ctcl-bregis/mct2/full/case/mct2_smec_smd.scad

// MediaCow Touch 2 - CTCL 2021-2025
// Purpose: SMEC display mount
// Created: February 12, 2025
// Modified: February 12, 2025
