ctcl-bregis/mct2/circuits/mct2/mct2_power.kicad_sch

## KiCad design circuits/mct2/mct2_power.kicad_sch (2024-09-12)

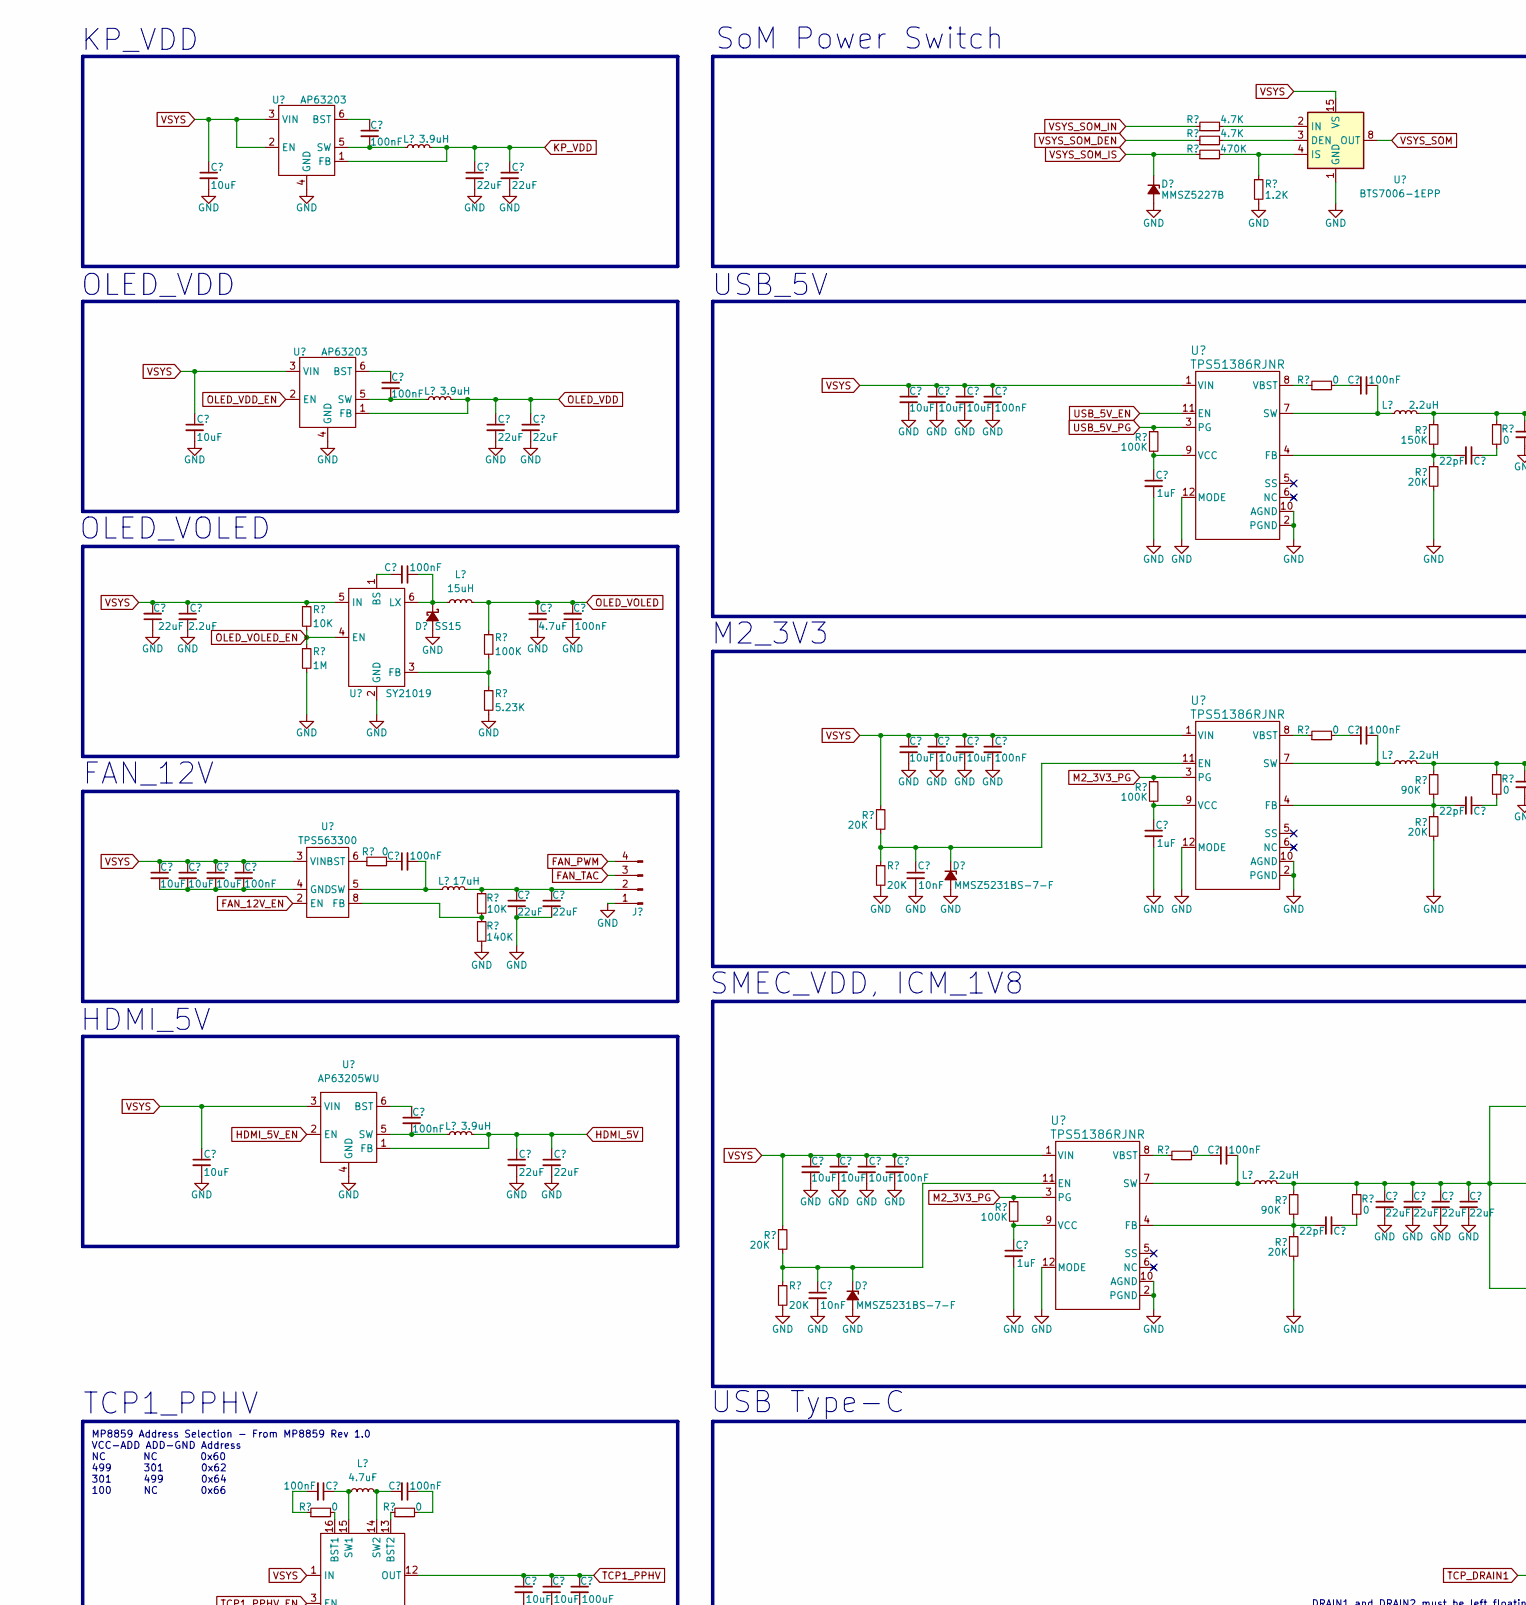
[picture p9: schematic mct2_power.kicad_sch, part in row 1, column 1]

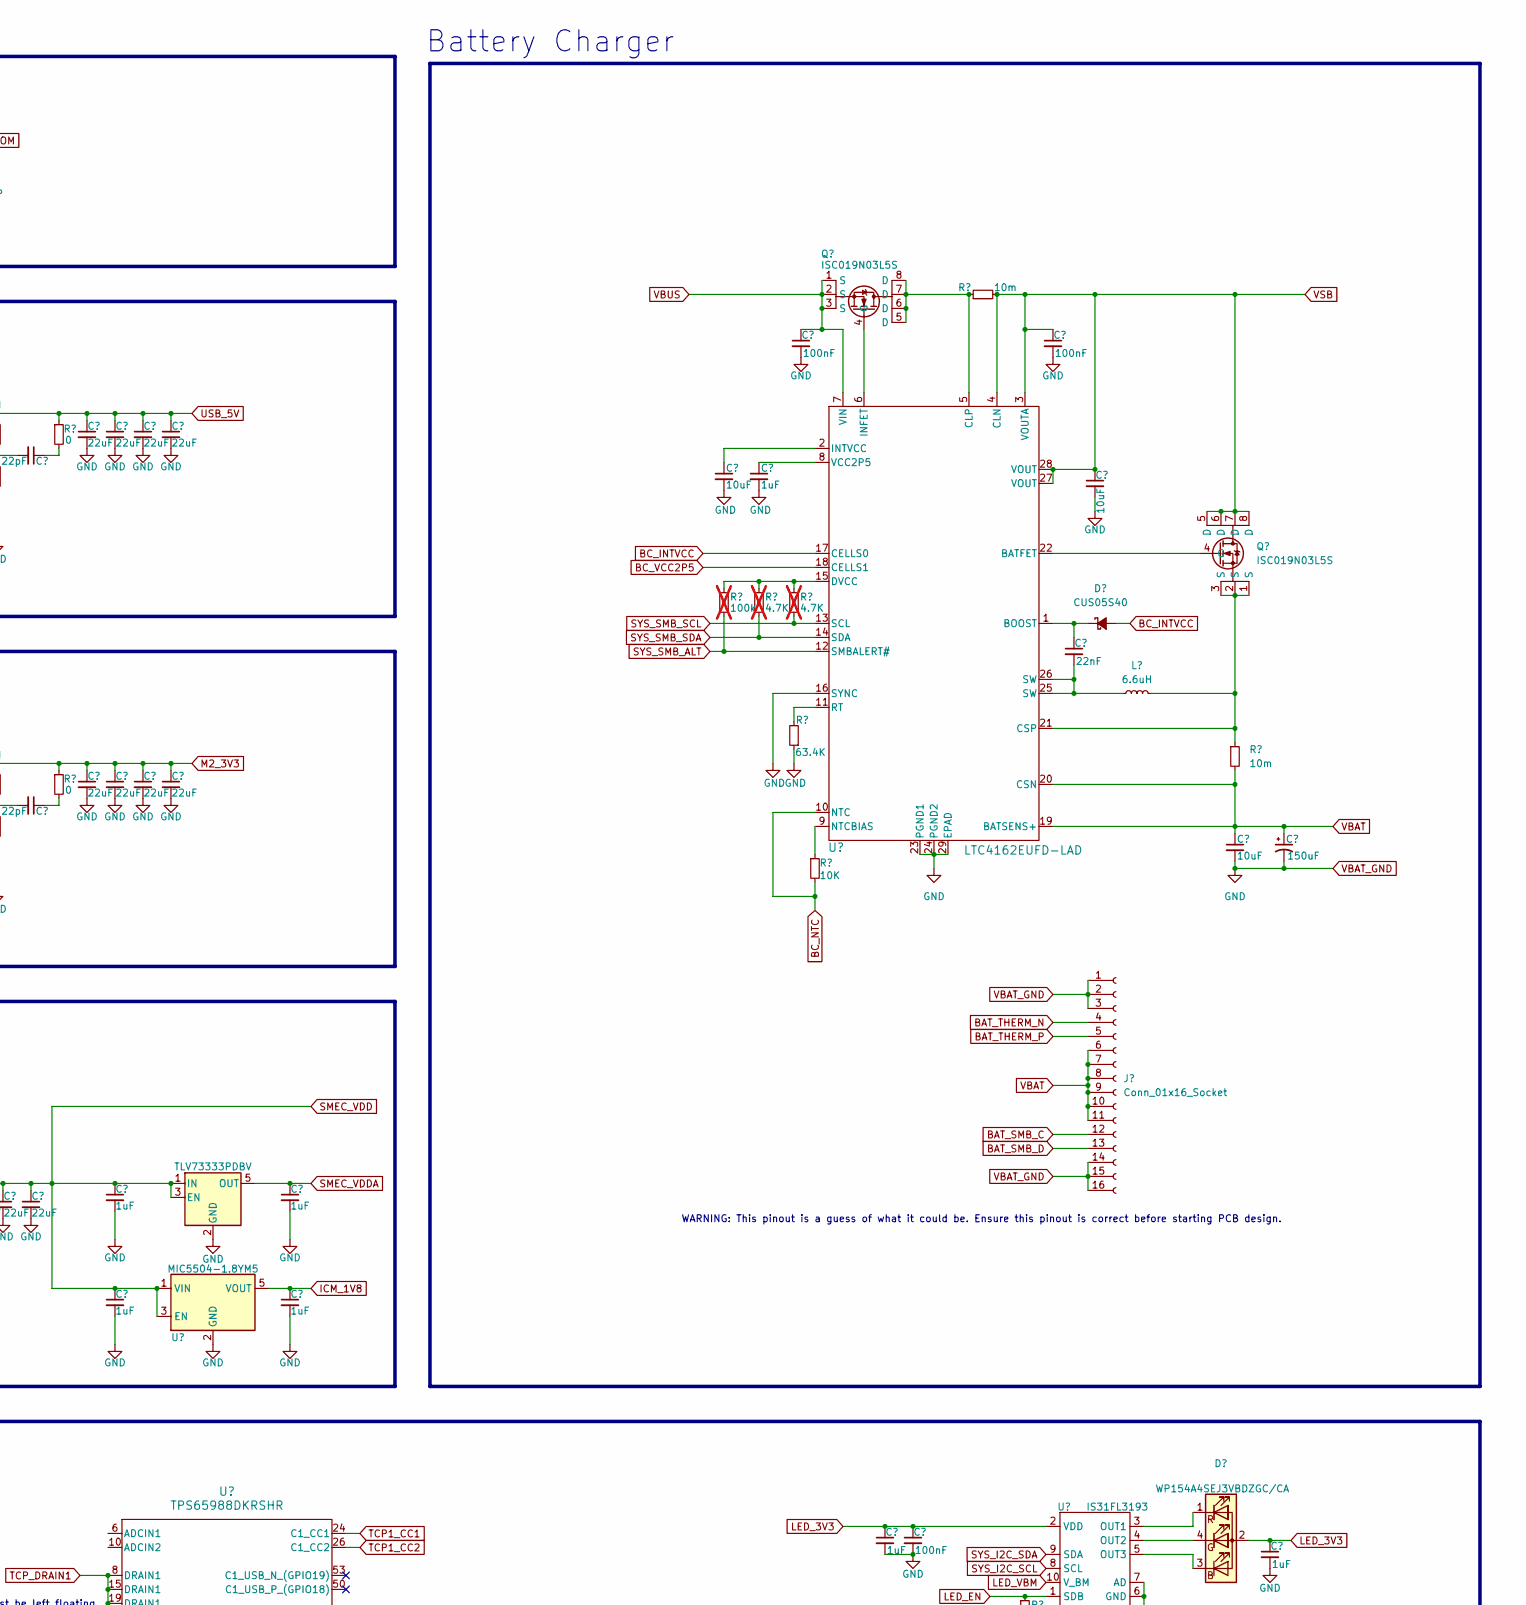
[picture p10: schematic mct2_power.kicad_sch, part in row 1, column 2]

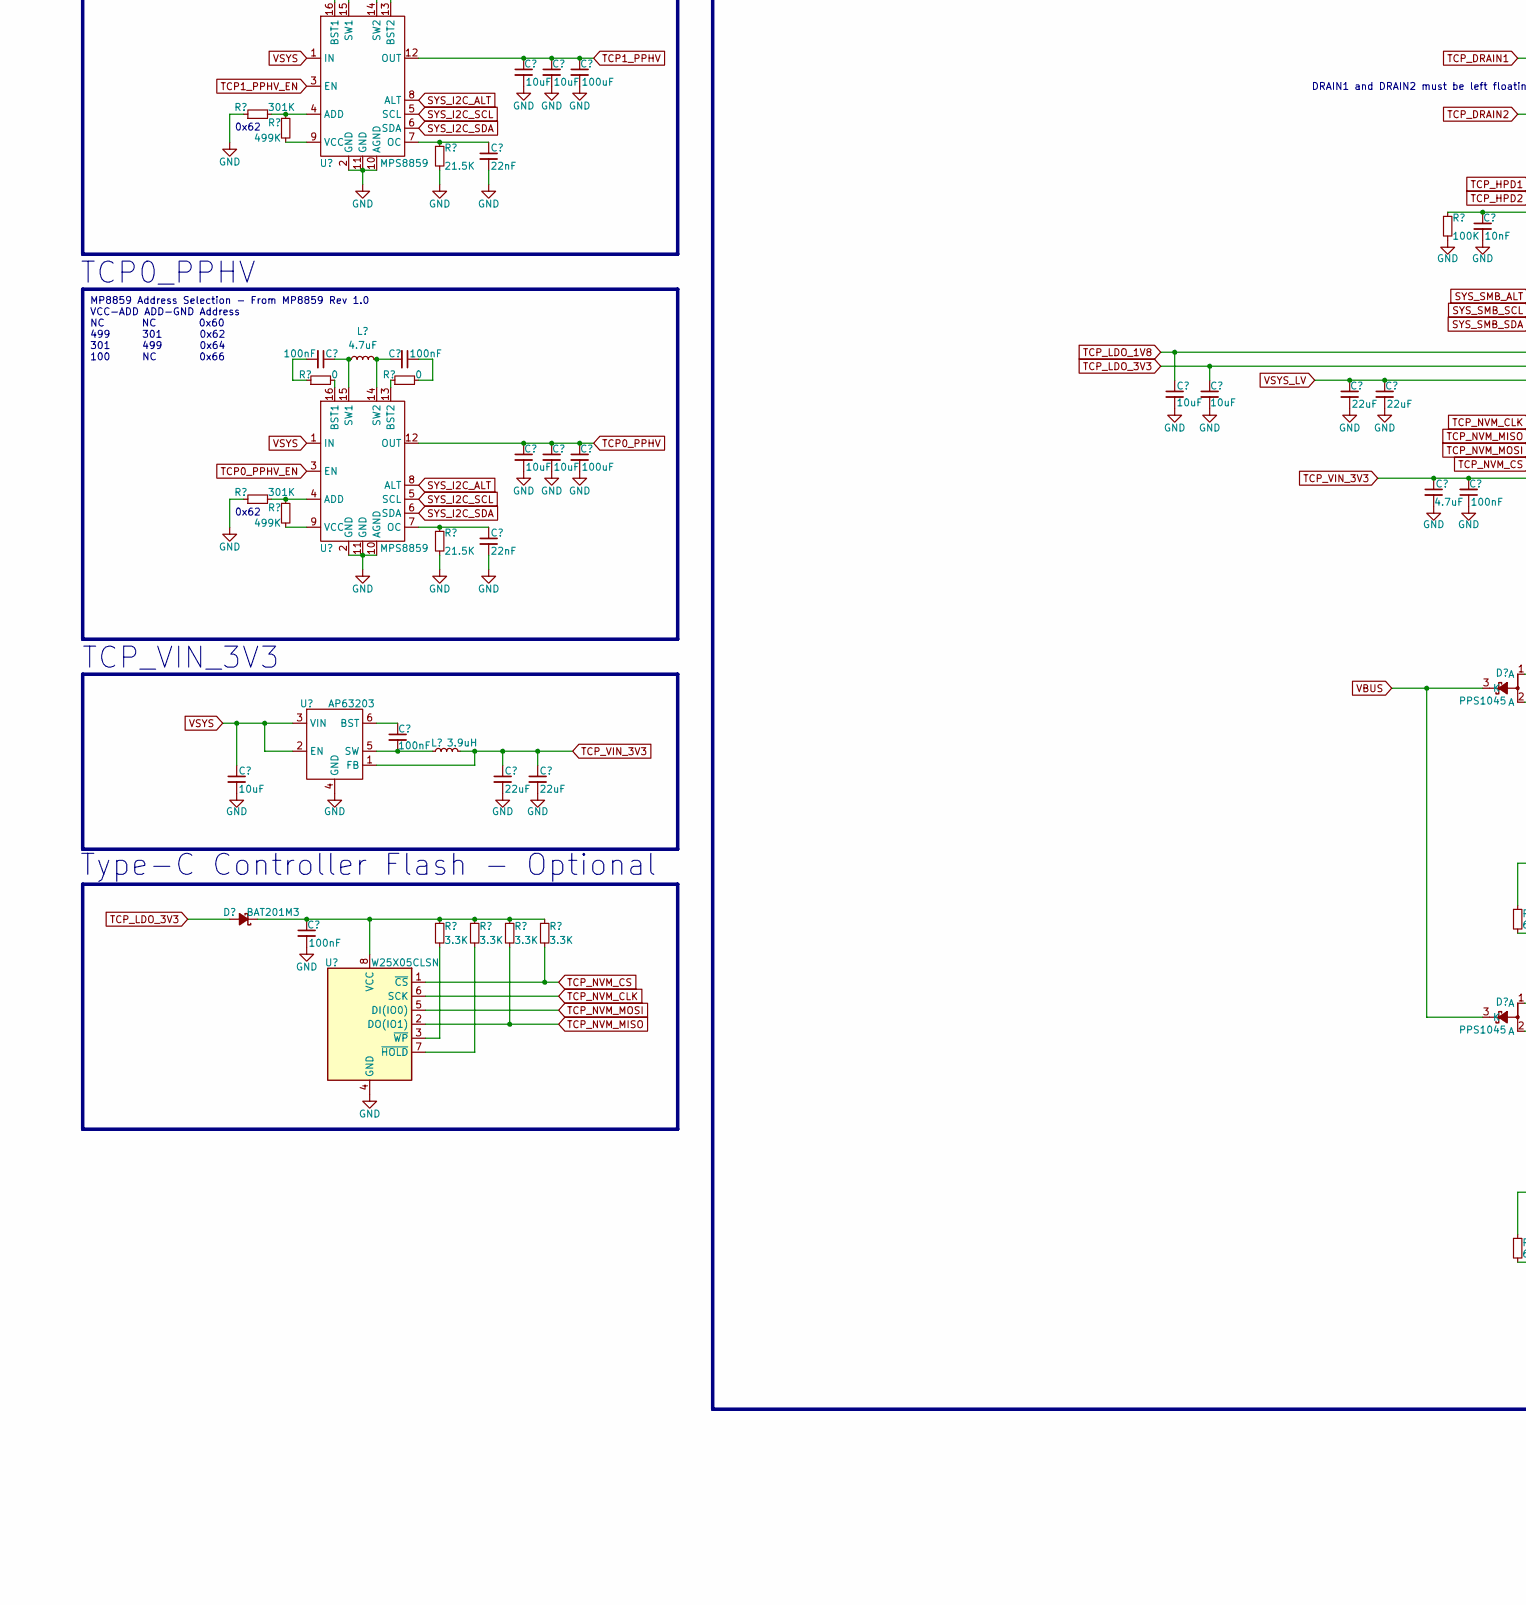
[picture p11: schematic mct2_power.kicad_sch, part in row 2, column 1]

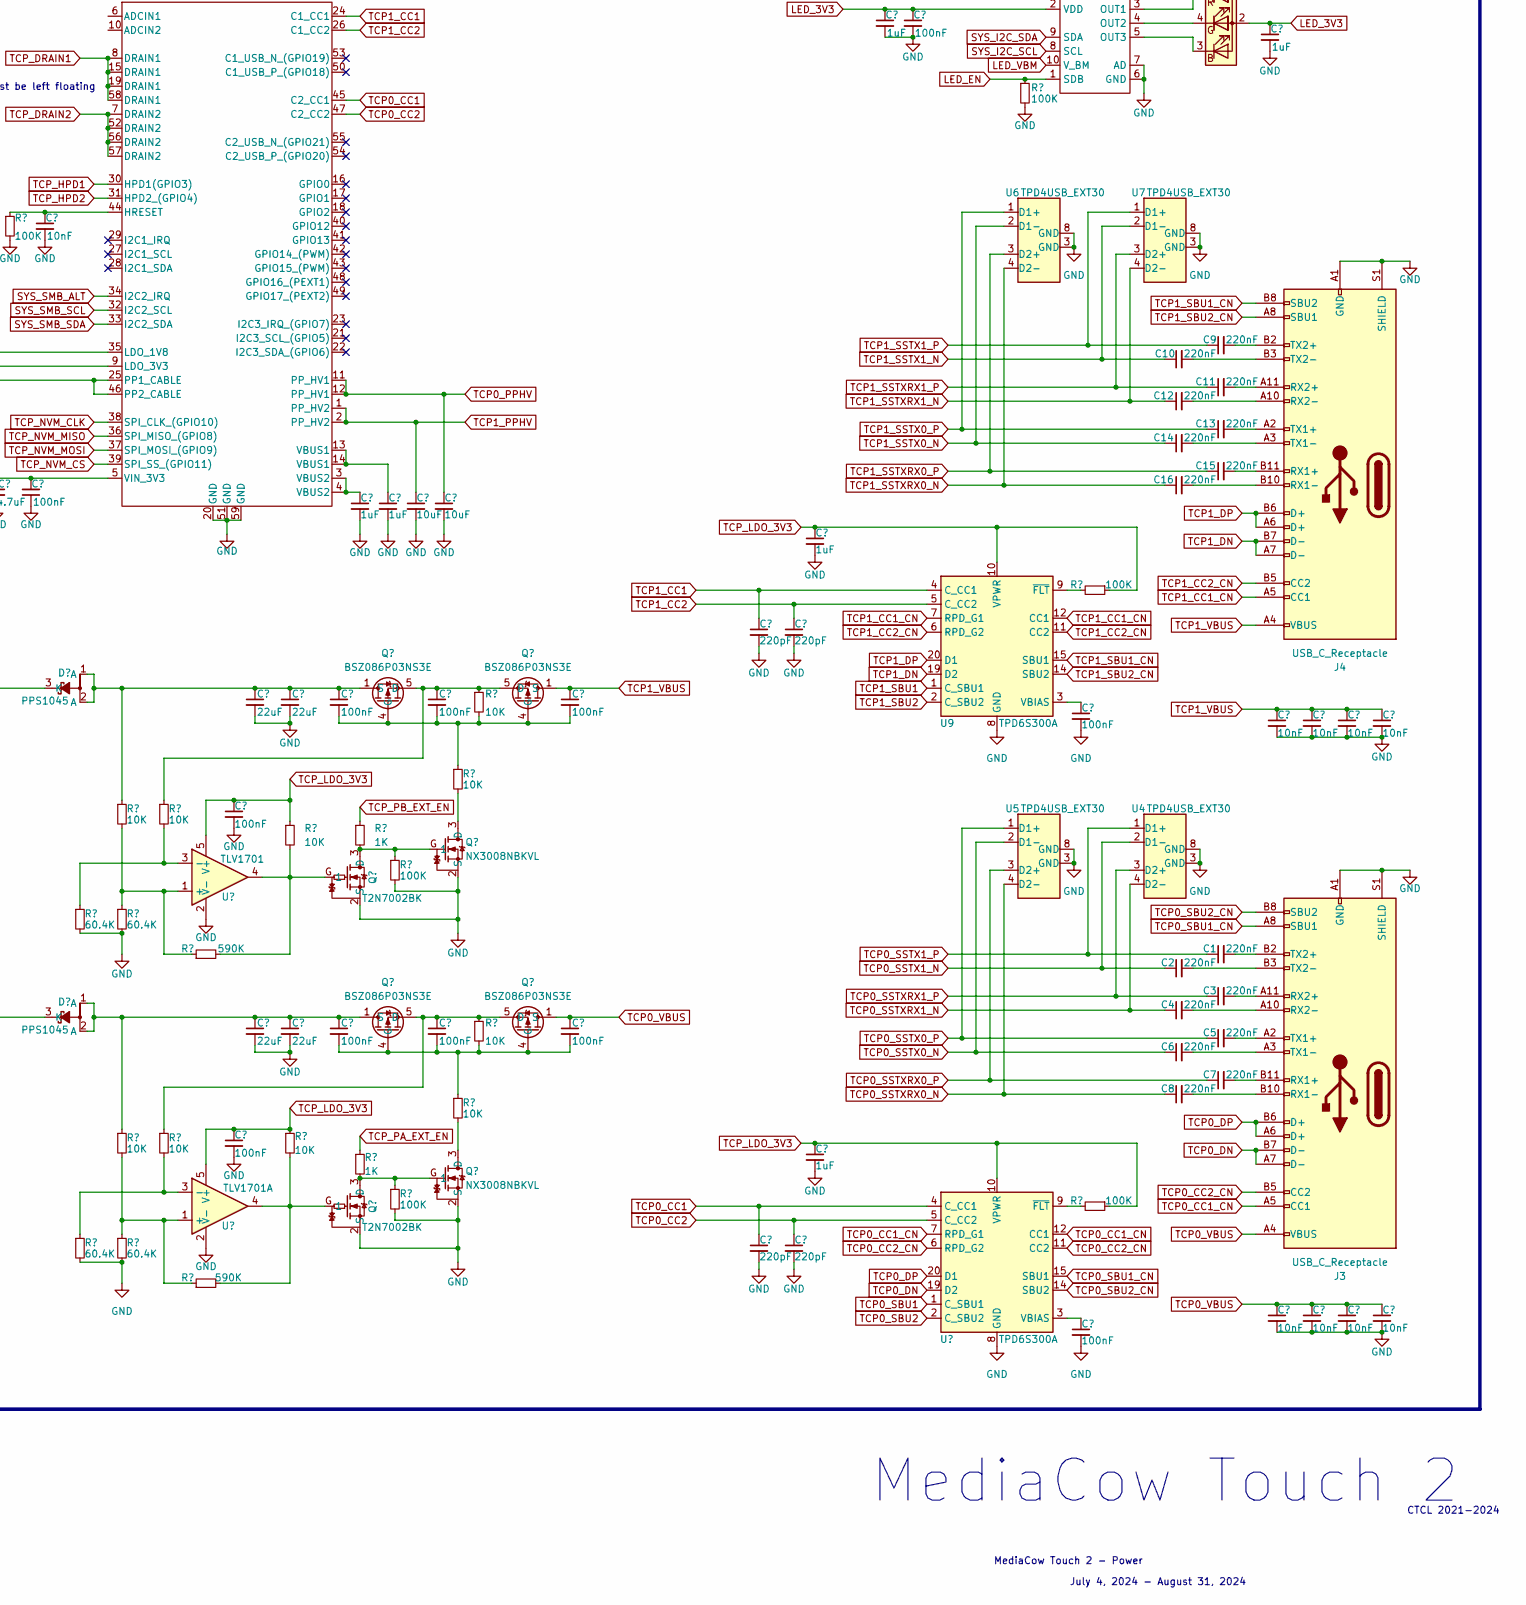
[picture p12: schematic mct2_power.kicad_sch, part in row 2, column 2]

Parts:
C1, C2, C3, C4, C5, C6, C7, C8, C9, C10, C11, C12, C13, C14, C15, C16: 220nF; C_0603_1608Metric
J3, J4: USB_C_Receptacle
U4, U5, U6, U7: TPD4USB_EXT30; USON-10_2.5x1.0mm_P0.5mm
U9: TPD6S300A; WQFN-20-1EP_3x3mm_P0.4mm_EP1.7x1.7mm_ThermalVias

Connections:
GND: J3.A1 (GND), J3.A12 (GND), J3.B1 (GND), J3.B12 (GND), J3.S1 (SHIELD), J4.A1 (GND), J4.A12 (GND), J4.B1 (GND), J4.B12 (GND), J4.S1 (SHIELD), U4.3 (D2+), U4.8 (GND), U5.3 (D2+), U5.8 (GND), U6.3 (D2+), U6.8 (GND), U7.3 (D2+), U7.8 (GND), U9.8 (GND), U9.13 (GND), U9.16 (GND), U9.17 (GND), U9.18 (GND), U9.21 (GND)
unnamed: C1.2, J3.B2 (TX2+)
unnamed: C2.2, J3.B3 (TX2-)
unnamed: C3.2, J3.A11 (RX2+)
unnamed: C4.2, J3.A10 (RX2-)
unnamed: C5.2, J3.A2 (TX1+)
unnamed: C6.2, J3.A3 (TX1-)
unnamed: C7.2, J3.B11 (RX1+)
unnamed: C8.2, J3.B10 (RX1-)
unnamed: C9.2, J4.B2 (TX2+)
unnamed: C10.2, J4.B3 (TX2-)
unnamed: C11.2, J4.A11 (RX2+)
unnamed: C12.2, J4.A10 (RX2-)
unnamed: C13.2, J4.A2 (TX1+)
unnamed: C14.2, J4.A3 (TX1-)
unnamed: C15.2, J4.B11 (RX1+)
unnamed: C16.2, J4.B10 (RX1-)
TCP0_CC1_CN: J3.A5 (CC1)
TCP0_CC2_CN: J3.B5 (CC2)
TCP0_DN: J3.A7 (D-), J3.B7 (D-)
TCP0_DP: J3.A6 (D+), J3.B6 (D+)
TCP0_SBU1_CN: J3.A8 (SBU1)
TCP0_SBU2_CN: J3.B8 (SBU2)
TCP0_SSTX0_N: C6.1, U5.2 (D1-)
TCP0_SSTX0_P: C5.1, U5.1 (D1+)
TCP0_SSTX1_N: C2.1, U4.2 (D1-)
TCP0_SSTX1_P: C1.1, U4.1 (D1+)
TCP0_SSTXRX0_N: C8.1, U5.4 (D2-)
TCP0_SSTXRX0_P: C7.1, U5.3 (D2+)
TCP0_SSTXRX1_N: C4.1, U4.4 (D2-)
TCP0_SSTXRX1_P: C3.1, U4.3 (D2+)
TCP0_VBUS: J3.A4 (VBUS), J3.A9 (VBUS), J3.B4 (VBUS), J3.B9 (VBUS)
TCP1_CC1: U9.4 (C_CC1)
TCP1_CC1_CN: J4.A5 (CC1), U9.7 (RPD_G1), U9.12 (CC1)
TCP1_CC2: U9.5 (C_CC2)
TCP1_CC2_CN: J4.B5 (CC2), U9.6 (RPD_G2), U9.11 (CC2)
TCP1_DN: J4.A7 (D-), J4.B7 (D-), U9.19 (D2)
TCP1_DP: J4.A6 (D+), J4.B6 (D+), U9.20 (D1)
TCP1_SBU1: U9.1 (C_SBU1)
TCP1_SBU1_CN: J4.B8 (SBU2), U9.15 (SBU1)
TCP1_SBU2: U9.2 (C_SBU2)
TCP1_SBU2_CN: J4.A8 (SBU1), U9.14 (SBU2)
TCP1_SSTX0_N: C14.1, U6.2 (D1-)
TCP1_SSTX0_P: C13.1, U6.1 (D1+)
TCP1_SSTX1_N: C10.1, U7.2 (D1-)
TCP1_SSTX1_P: C9.1, U7.1 (D1+)
TCP1_SSTXRX0_N: C16.1, U6.4 (D2-)
TCP1_SSTXRX0_P: C15.1, U6.3 (D2+)
TCP1_SSTXRX1_N: C12.1, U7.4 (D2-)
TCP1_SSTXRX1_P: C11.1, U7.3 (D2+)
TCP1_VBUS: J4.A4 (VBUS), J4.A9 (VBUS), J4.B4 (VBUS), J4.B9 (VBUS)
TCP_LDO_3V3: U9.10 (VPWR)

Notes on the sheet:
CTCL 2021-2024
TCP0_PPHV
DRAIN1 and DRAIN2 must be left floating
Type-C Controller Flash - Optional
0x62
FAN_12V
USB_5V
WARNING: This pinout is a guess of what it could be. Ensure this pinout is correct before starting PCB design.
OLED_VDD
Battery Charger
KP_VDD
MediaCow Touch 2 - Power
MediaCow Touch 2
TCP_VIN_3V3
USB Type-C
SMEC_VDD, ICM_1V8
HDMI_5V
MP8859 Address Selection - From MP8859 Rev 1.0 VCC-ADD ADD-GND Address NC NC 0x60 499 301 0x62 301 499 0x64 100 NC 0x66
SoM Power Switch
OLED_VOLED
M2_3V3
July 4, 2024 - August 31, 2024
TCP1_PPHV
